mlorenzati/pico-rgb2hdmi/docs/A600_CSYNC_CH1_VSYNC_CH2.png

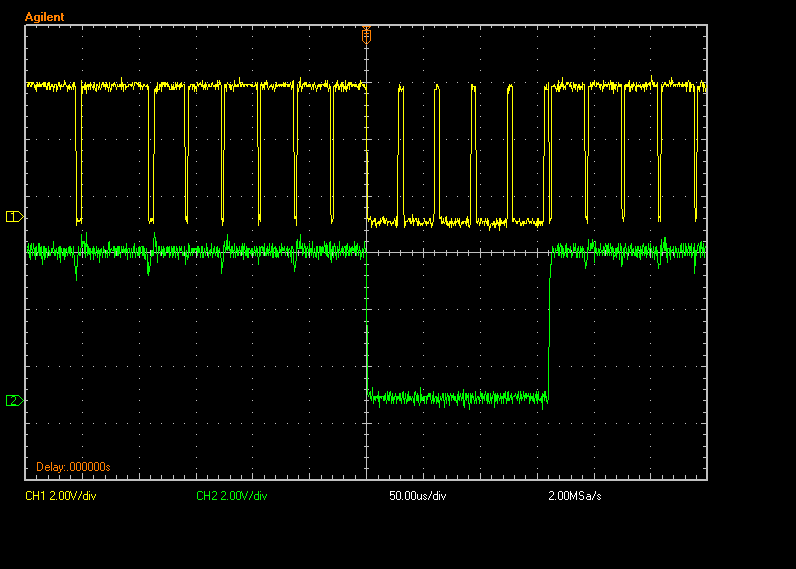
docs/A600_CSYNC_CH1_VSYNC_CH2.png
