mlorenzati/pico-rgb2hdmi/tools/images/file_320_240_16.png

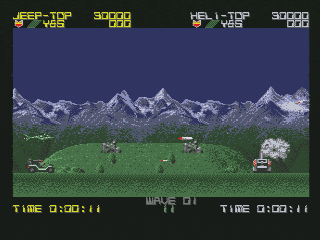
tools/images/file_320_240_16.png
