mlorenzati/pico-rgb2hdmi/tools/images/file_640_240_8.png

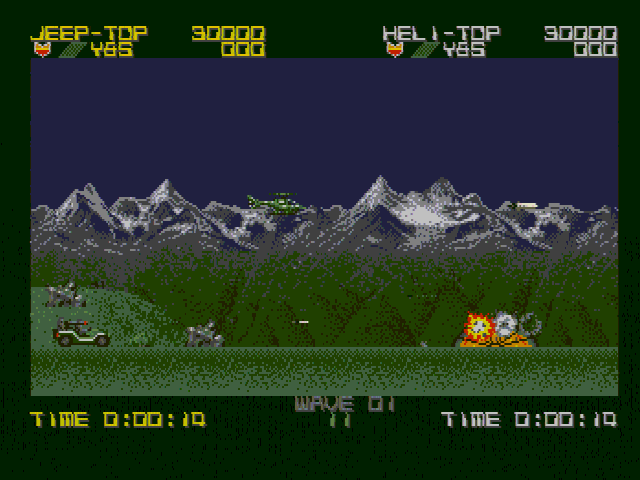
tools/images/file_640_240_8.png
