mlorenzati/pico-rgb2hdmi/tools/images/Font_64.gif

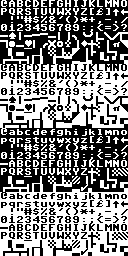
tools/images/Font_64.gif
