mlorenzati/pico-rgb2hdmi/src/rgbScan/nanoSystick.h

/*
*/
#ifndef _NANO_SYSTICK_H
#define _NANO_SYSTICK_H

#include "hardware/structs/systick.h"
// Systick Info: https://developer.arm.com/documentation/dui0497/a/cortex-m0-peripherals/optional-system-timer--systick/systick-control-and-status-register

#define NANO_SYSTICK_MAX_COUNTERS 2

typedef struct {
    io_rw_32 enable:1;      // Enable SysTick counter
    io_rw_32 tickint:1;     // Enables SysTick exception request
    io_rw_32 clksource:1;   // 0: external, 1: internal
    io_rw_32 reserved:13;
    io_rw_32 countflag:1;   // Returns 1 if timer counted to 0 since last time this was read
} *systick_csr;

typedef struct {
    io_rw_32 reload:24;
} *systick_rvr;

typedef struct {
    io_rw_32 current:24;
} *systick_cvr;

typedef struct {
    io_rw_32 tenms:24;
    io_rw_32 reserved:6;
    io_rw_32 skew:1;
    io_rw_32 noref:1;
} *systick_calibration_r;

extern systick_cvr systick_current;
extern systick_csr systick_control;
extern uint32_t nanoSystick_timestampLast[NANO_SYSTICK_MAX_COUNTERS];

#define systick_delta(last, current) (last - current)&0xFFFFFF;
int systick_setup(bool useInterrupts);
int systick_start(bool wait, uint32_t ticks);

static inline io_rw_32 systick_get_current() {
    return systick_current->current;
}

 
static inline io_rw_32 systick_mark(unsigned char id) {
    io_rw_32 current = systick_current->current;
    io_rw_32 delta = systick_delta(nanoSystick_timestampLast[id], current);
    nanoSystick_timestampLast[id] = current;

    return delta;
}

static inline uint32_t systick_stop(unsigned char id) {
    uint32_t delta = systick_mark(id);
    systick_control->enable = 0; 
    return delta;
}

#endif//_NANO_SYSTICK_H
